hagleitn/stillgood/simulator.cpp

#ifdef SIM

#include "simulator.h"

/**
   This file is just a simple wrapper around the actual arduino file
   to run w/o a board. It mocks a bunch of arduino functions to be
   able to compile the sketch and print out the results of running the
   program.
*/

unsigned long _millis = 0;

unsigned long millis() {
  // wrap around every 50 days
  return _millis % (1000ul*60ul*60ul*24ul*50ul);
}

int digitalPinToInterrupt(int p) {
  return 0;
}

void (*_a)(); // reset callback

void attachInterrupt(int p, void (*a)(), int m) {
  _a = a;
}

void pinMode(int p, int m) {
  char *mode;

  if (m == 0) mode = (char *)"OUTPUT";
  if (m == 1) mode = (char *)"INPUT";
  if (m == 2) mode = (char *)"INPUT_PULLUP";
  printf("Pin %i: %s\n", p, mode);
}

int cnt = 0;
int cnt2 = 0;
int last = 0;
int lastPair[2] = {-1,-1};
byte b = 0x01 << 6;
extern byte codes[10];
extern int segmentSelector[DIGITS];

int pinValue = HIGH;
int digitalRead(int p) {
  pinValue = pinValue == HIGH ? LOW : HIGH;
  return pinValue;
}

/**
   These writes are used for the 7 segment display only. So every 7
   writes look up what was printed.
*/
void digitalWrite(int p, int v) {
  v = v == HIGH ? LOW : HIGH;

  if (segmentSelector[0] != p && segmentSelector[1] != p) {
    b = (b>>1) | (v<<6);
    if (++cnt == 7) {
      cnt = 0;
      for (int i = 0; i < 10; i++) {
        if (codes[i] == b) {
          if (++cnt2 == 2) {
            if (lastPair[0] != i || lastPair[1] != last) {
              printf("%i%i\n",i,last);
              lastPair[0] = i;
              lastPair[1] = last;
            }
            cnt2 = 0;
          }
          last = i;
        }
      }
      b = 0x00;
    }
  }
}

void delay(int p) {
  _millis += p;
}

void setup();
void loop();
void reset();

int main(int argc, char **argv) {

  setup();

  for (int i = 1; i < 3; i++) {

    // simulate 200 days of runtime
    while(_millis < i*200ul*1000*60*60*24) {
      _millis += 200;
      loop();
    }

    // simulate pressing the reset.
    _a();
  }
  return 0;
}
#include "still_good.ino"
#endif
